Maxr1998/Phoebe_Keyboard/case_v2/plate.scad

include <spec.scad>;

module plate() {
  color("silver") {
    linear_extrude(height = plate_thickness) {
      import("plate.dxf");
    }
  }
}
